ccadic/ESP32-S2-DevBoardTFT/esp32-addons/devshield/images/ESP32-S2-WROOMb.jpg

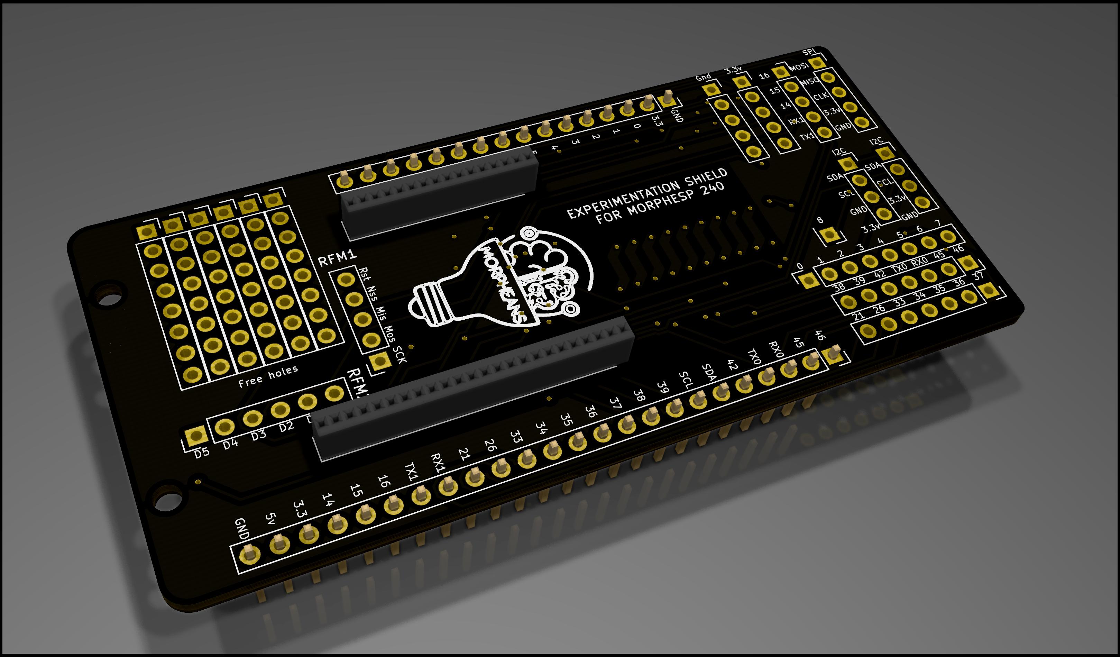
esp32-addons/devshield/images/ESP32-S2-WROOMb.jpg
