ccadic/ESP32-S2-DevBoardTFT/esp32-addons/leather-holder/etui3.JPG

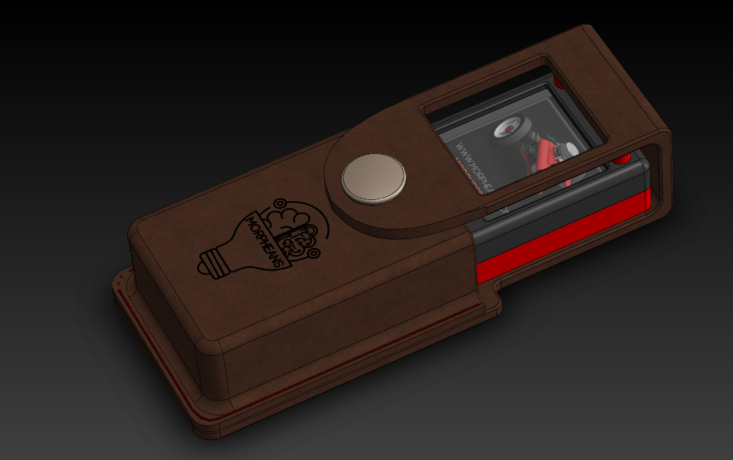
esp32-addons/leather-holder/etui3.JPG
