ccadic/ESP32-S2-DevBoardTFT/esp32-addons/leather-holder/etui4.JPG

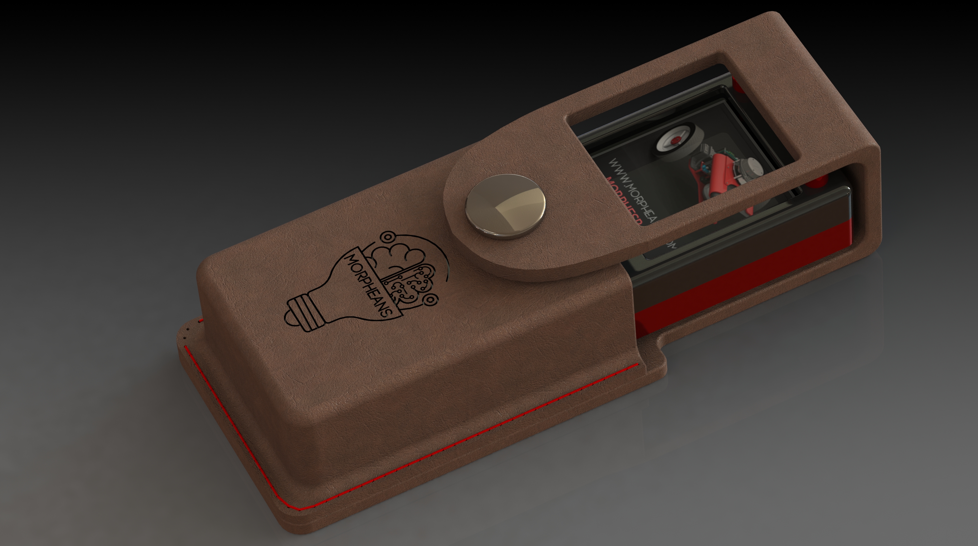
esp32-addons/leather-holder/etui4.JPG
