ccadic/ESP32-S2-DevBoardTFT/photo-gallery/20200802_192520.jpg

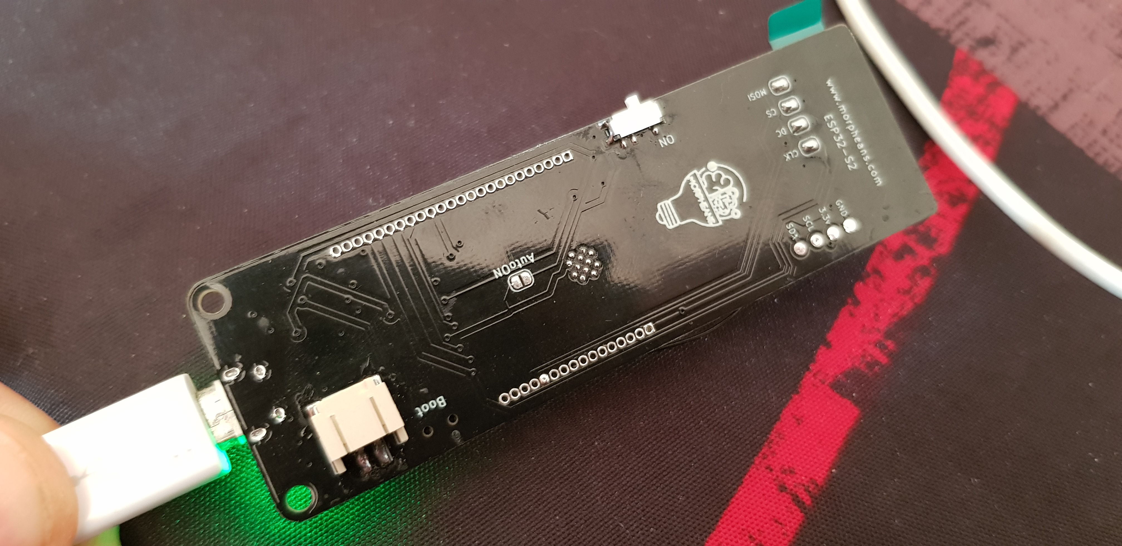
photo-gallery/20200802_192520.jpg
