ccadic/ESP32-S2-DevBoardTFT/photo-gallery/eldiablo2s2.JPG

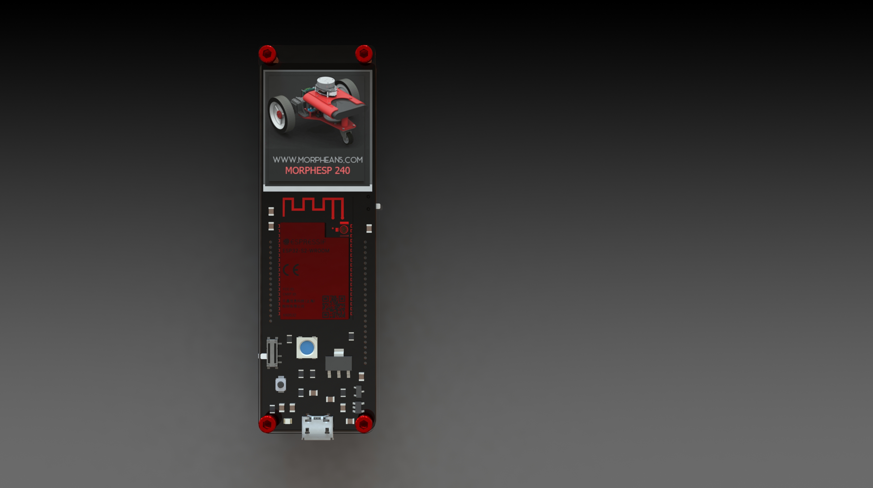
photo-gallery/eldiablo2s2.JPG
