ccadic/ESP32-S2-DevBoardTFT/photo-gallery/eldiablo2s4.JPG

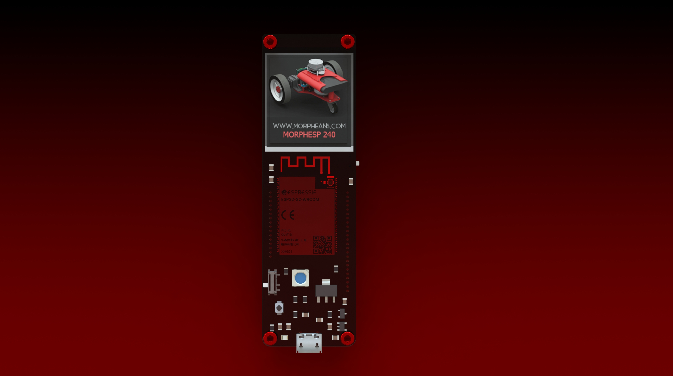
photo-gallery/eldiablo2s4.JPG
