ccadic/ESP32-S2-DevBoardTFT/photo-gallery/ESP32-S2-SOLIDWORKS.JPG

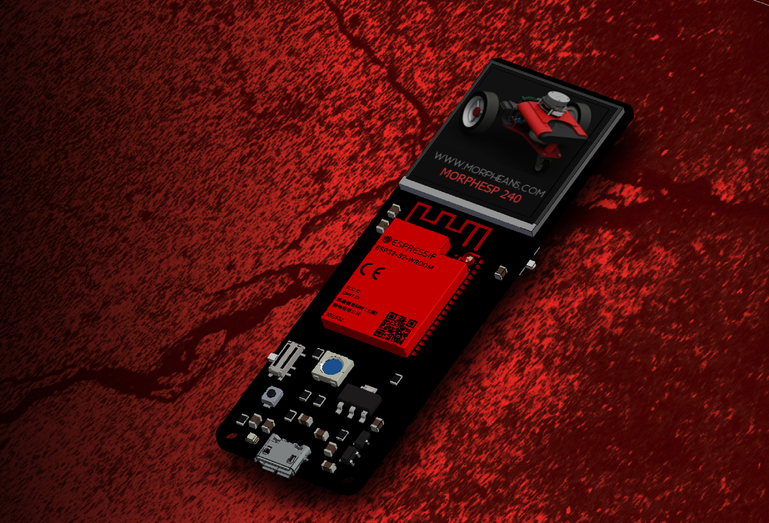
photo-gallery/ESP32-S2-SOLIDWORKS.JPG
