ccadic/ESP32-S2-DevBoardTFT/photo-gallery/etui9.JPG

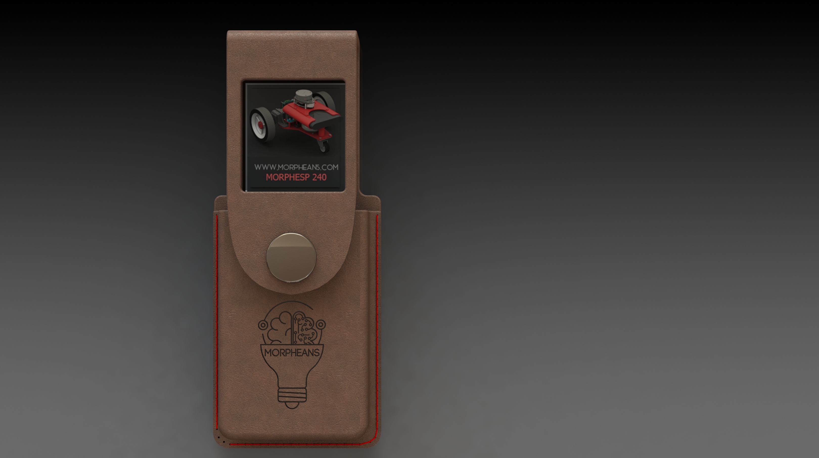
photo-gallery/etui9.JPG
