ccadic/ESP32-S2-DevBoardTFT/photo-gallery/etui11.JPG

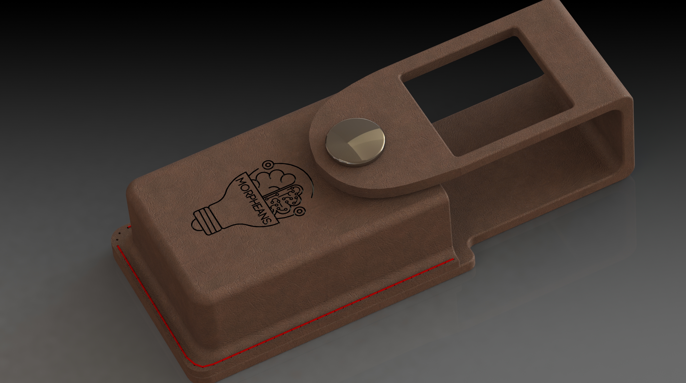
photo-gallery/etui11.JPG
