ccadic/ESP32-S2-DevBoardTFT/photo-gallery/morphesp240-frontside-2-3D rendered.jpg

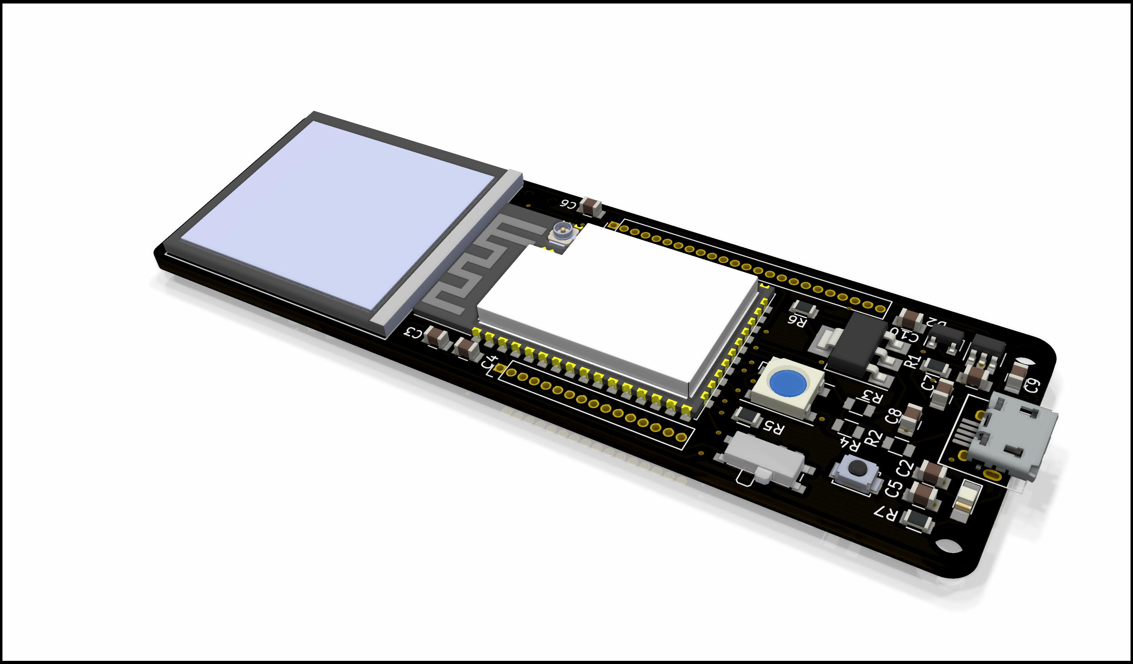
photo-gallery/morphesp240-frontside-2-3D rendered.jpg
