ccadic/ESP32-S2-DevBoardTFT/photo-gallery/morphesp240-pcboard-only.jpg

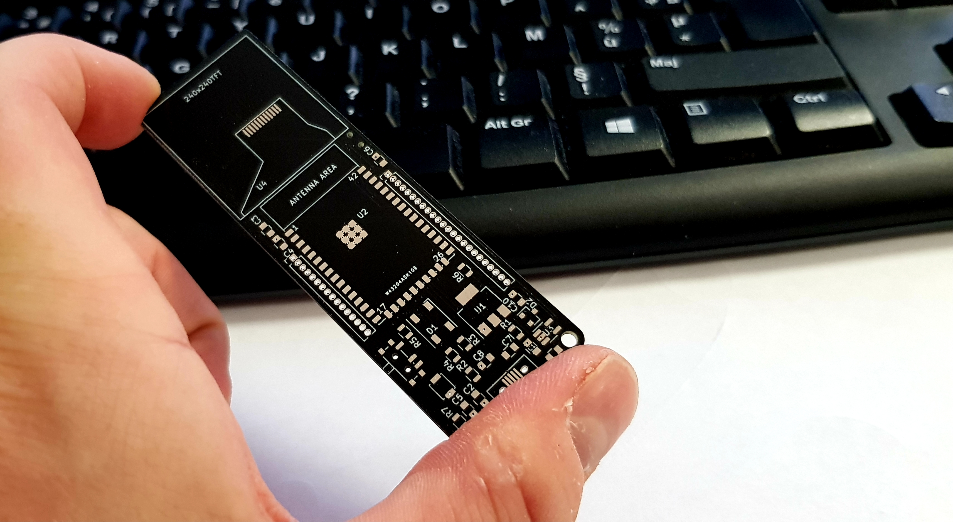
photo-gallery/morphesp240-pcboard-only.jpg
