ccadic/ESP32-S2-DevBoardTFT/esp32-addons/leather-holder/etuit.SLDPRT

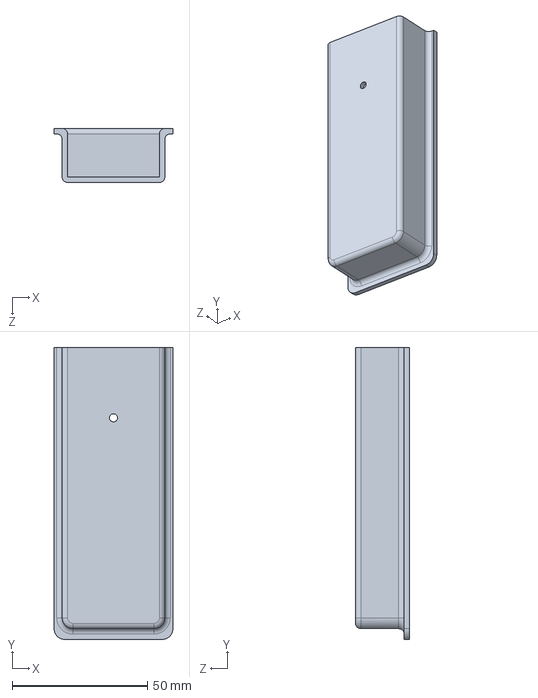
[picture p41: CAD file, 2020-08-18]
esp32-addons/leather-holder/etuit.SLDPRT
44.0 x 108.0 x 20.0 mm
