ccadic/ESP32-S2-DevBoardTFT/hardware/V3.1-LAST/3Dfiles/lipobat.STEP

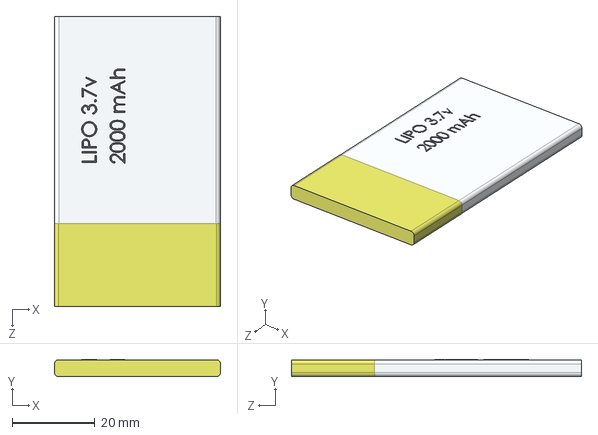
[picture p42: CAD file, 2020-08-18]
hardware/V3.1-LAST/3Dfiles/lipobat.STEP
40.1 x 4.12 x 70.0 mm
