ccadic/ESP32-S2-DevBoardTFT/esp32-addons/leather-holder/Line 20 Eyelet.SLDPRT

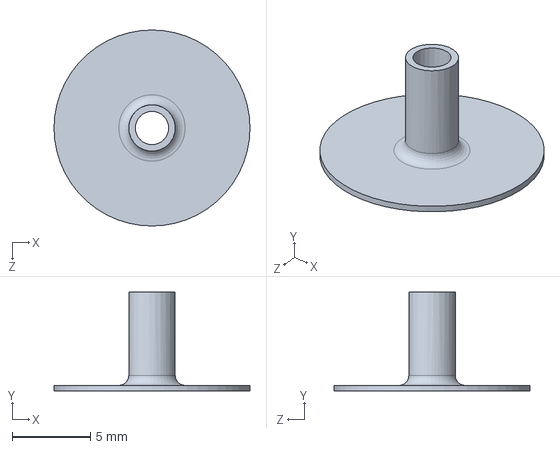
[picture p43: CAD file, 2020-08-18]
esp32-addons/leather-holder/Line 20 Eyelet.SLDPRT
12.5 x 6.32 x 12.5 mm
