ccadic/ESP32-S2-DevBoardTFT/hardware/V3.1-LAST/3Dfiles/JST-PH 2-Pin.STEP

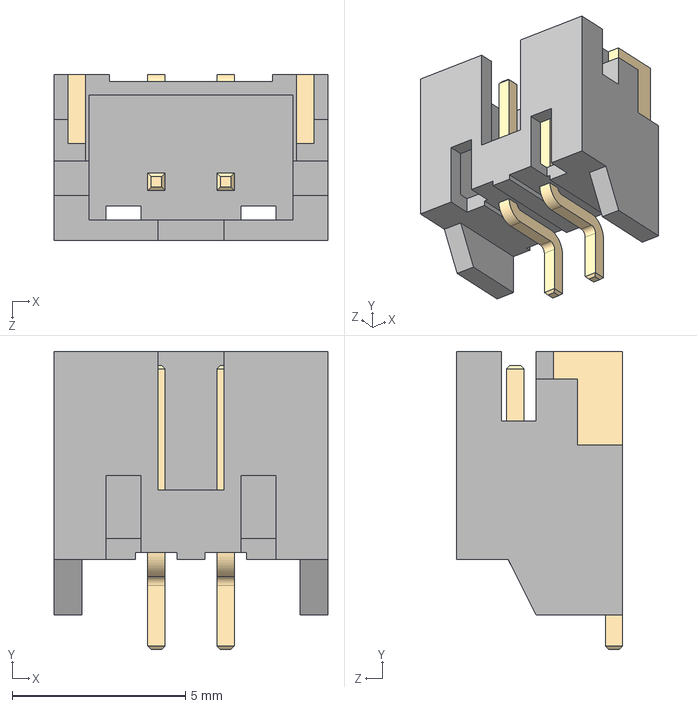
[picture p44: CAD file, 2020-08-18]
hardware/V3.1-LAST/3Dfiles/JST-PH 2-Pin.STEP
7.90 x 8.60 x 4.80 mm
