ccadic/ESP32-S2-DevBoardTFT/esp32-addons/leather-holder/couturecourve3.SLDPRT

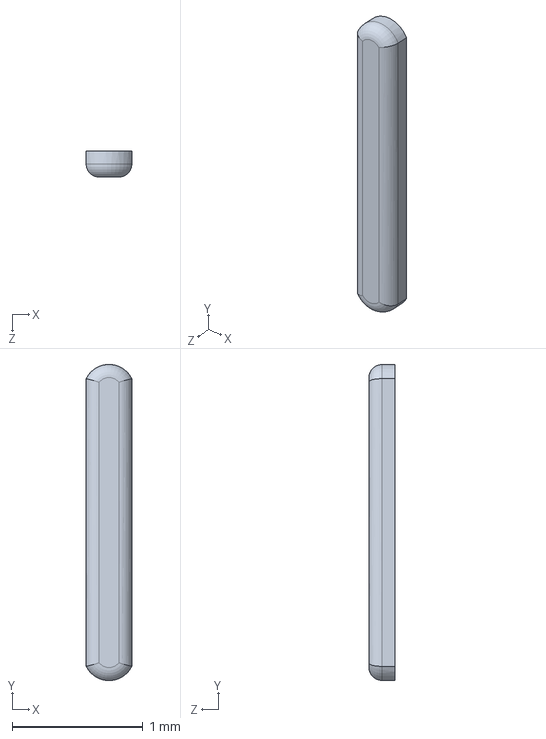
[picture p45: CAD file, 2020-08-18]
esp32-addons/leather-holder/couturecourve3.SLDPRT
0.35 x 2.42 x 0.2 mm
