ccadic/ESP32-S2-DevBoardTFT/esp32-addons/leather-holder/couturecourbe.SLDPRT

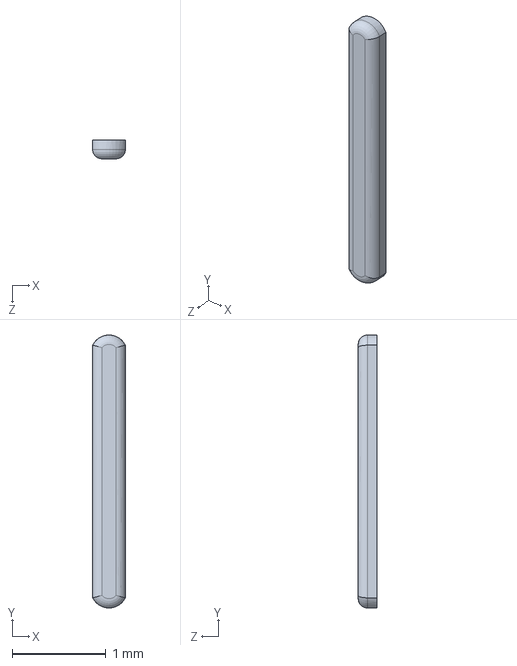
[picture p46: CAD file, 2020-08-18]
esp32-addons/leather-holder/couturecourbe.SLDPRT
0.35 x 2.92 x 0.2 mm
