ccadic/ESP32-S2-DevBoardTFT/hardware/V3.1-LAST/3Dfiles/PCM12SMTR.stp

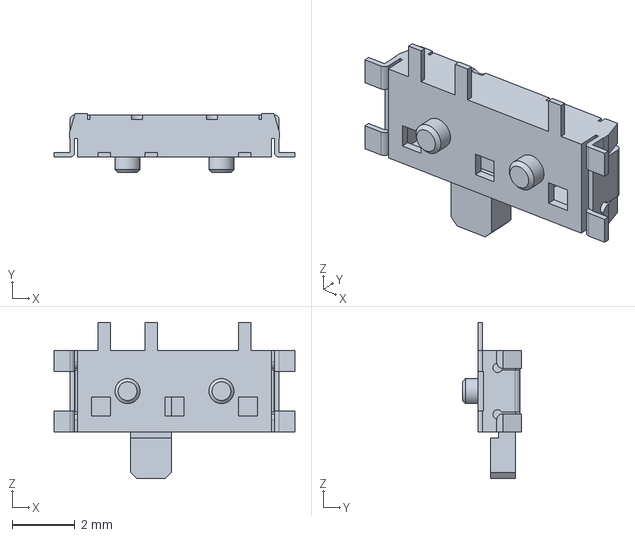
[picture p47: CAD file, 2020-08-18]
hardware/V3.1-LAST/3Dfiles/PCM12SMTR.stp
7.70 x 1.90 x 5.00 mm
