ccadic/ESP32-S2-DevBoardTFT/esp32-addons/leather-holder/Line 20 Cap.SLDPRT

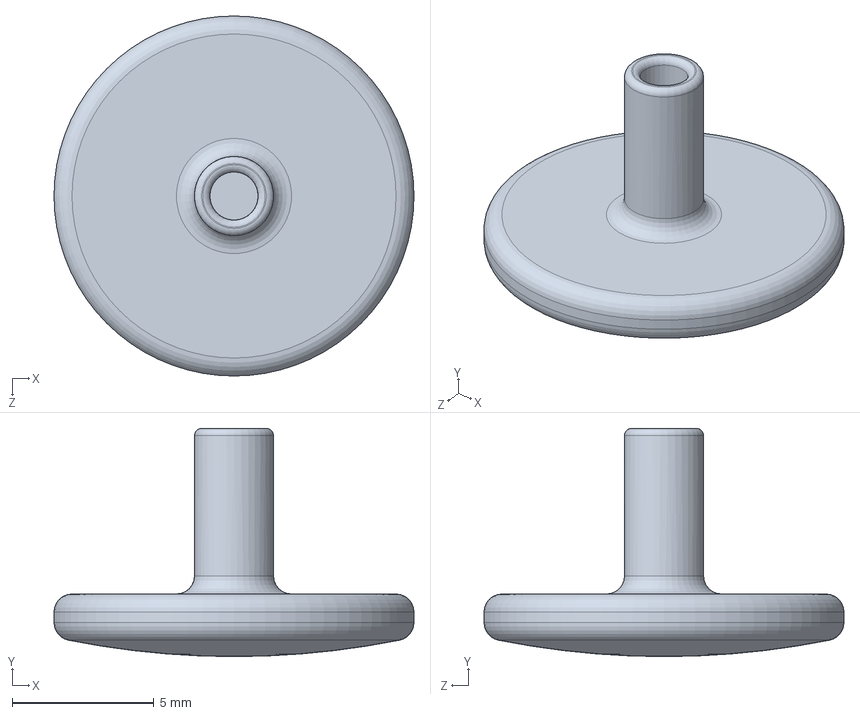
[picture p48: CAD file, 2020-08-18]
esp32-addons/leather-holder/Line 20 Cap.SLDPRT
12.7 x 8.05 x 12.7 mm
