ccadic/ESP32-S2-DevBoardTFT/hardware/V3.1-LAST/3Dfiles/JST-PH 2-Pin Breakout Board.STEP

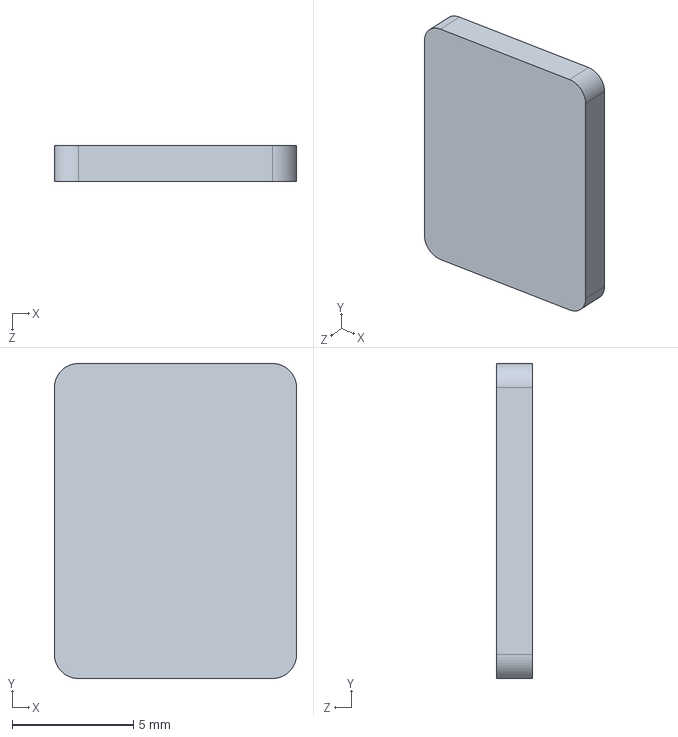
[picture p49: CAD file, 2020-08-18]
hardware/V3.1-LAST/3Dfiles/JST-PH 2-Pin Breakout Board.STEP
10.0 x 13.0 x 1.50 mm
