ccadic/ESP32-S2-DevBoardTFT/esp32-addons/leather-holder/supportcinture.SLDPRT

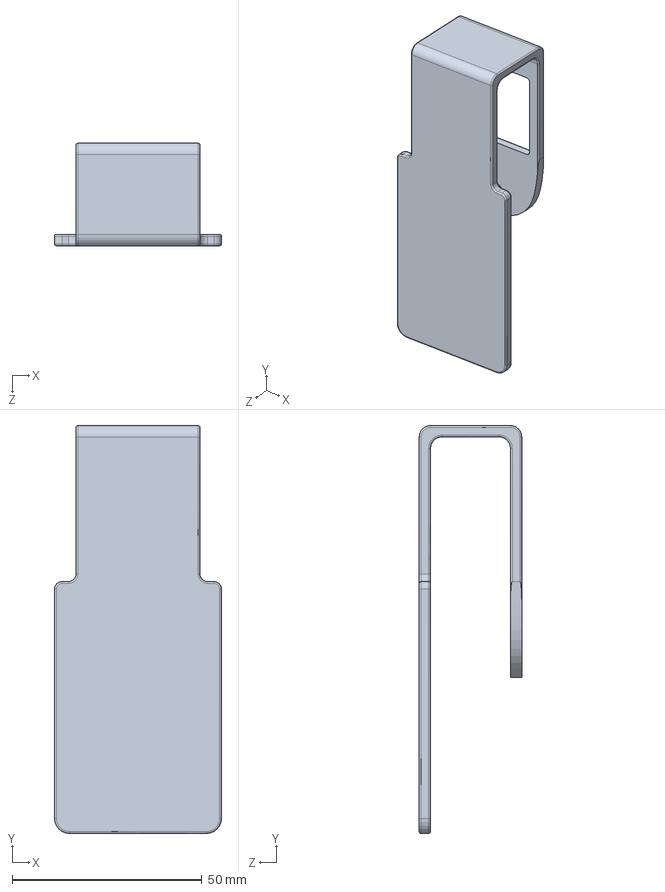
[picture p50: CAD file, 2020-08-18]
esp32-addons/leather-holder/supportcinture.SLDPRT
44.0 x 107.4 x 27.0 mm
