ccadic/ESP32-S2-DevBoardTFT/hardware/V3.1-LAST/3Dfiles/ESP32-S2-WROVER.STEP

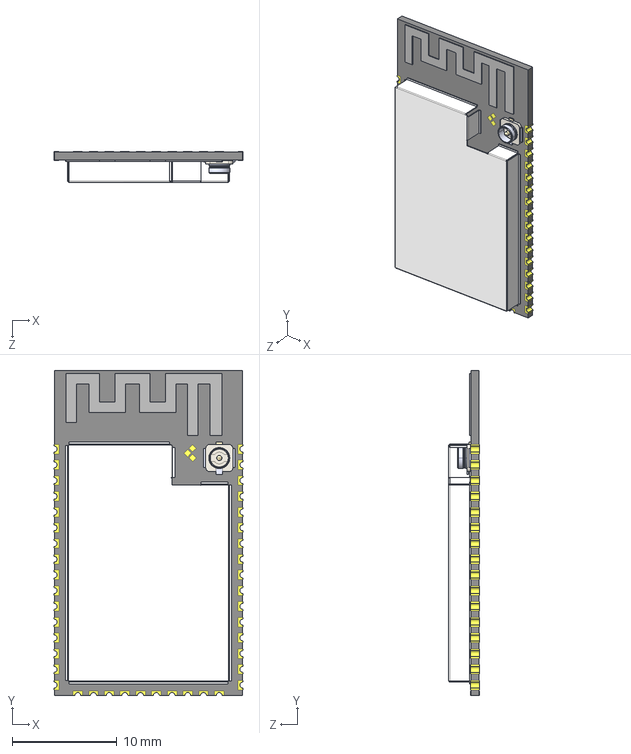
[picture p51: CAD file, 2020-08-02]
hardware/V3.1-LAST/3Dfiles/ESP32-S2-WROVER.STEP
18.0 x 31.0 x 2.91 mm
