ccadic/ESP32-S2-DevBoardTFT/esp32-addons/leather-holder/couture.SLDPRT

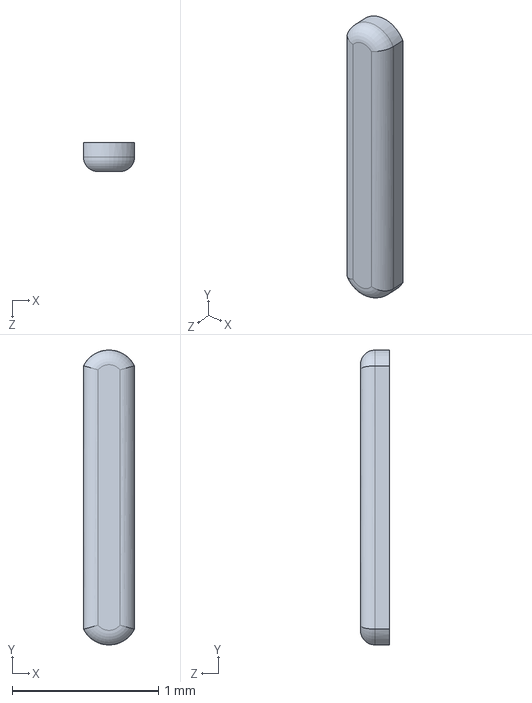
[picture p52: CAD file, 2020-08-18]
esp32-addons/leather-holder/couture.SLDPRT
0.35 x 2.02 x 0.2 mm
