ccadic/ESP32-S2-DevBoardTFT/hardware/V3.1-LAST/3Dfiles/micro_usb_connector.step

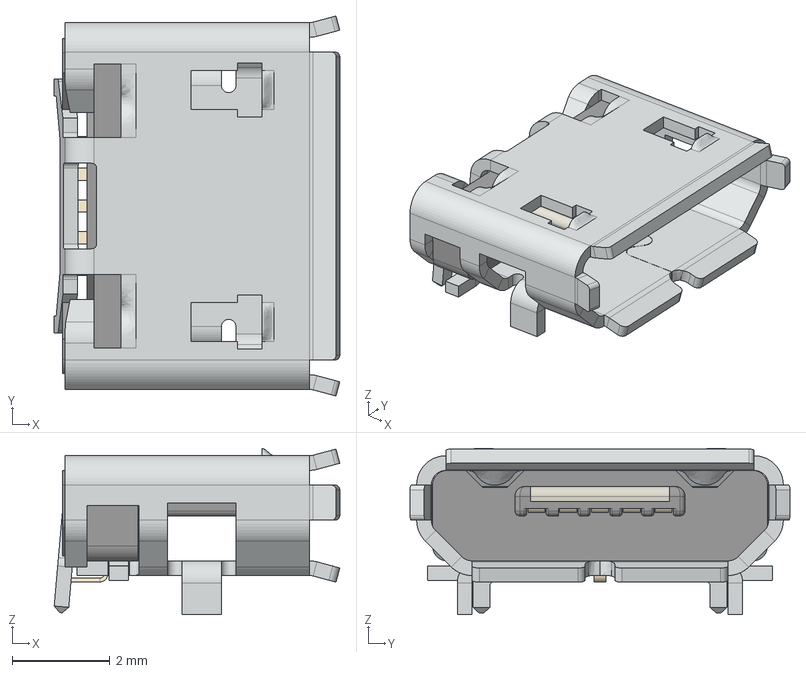
[picture p53: CAD file, 2020-08-02]
hardware/V3.1-LAST/3Dfiles/micro_usb_connector.step
5.84 x 7.77 x 3.40 mm
shield
socket_housing
socket_plate
terminal x 5
