ccadic/ESP32-S2-DevBoardTFT/esp32-addons/leather-holder/couture courbe2.SLDPRT

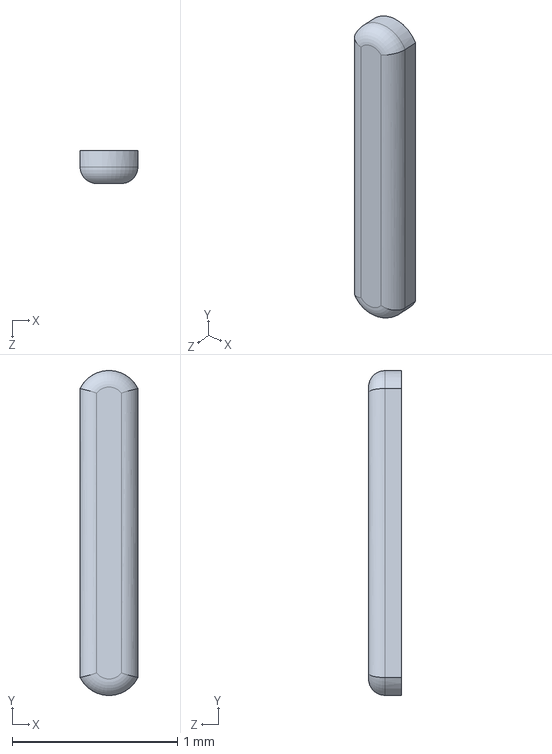
[picture p54: CAD file, 2020-08-18]
esp32-addons/leather-holder/couture courbe2.SLDPRT
0.35 x 1.97 x 0.2 mm
