ccadic/ESP32-S2-DevBoardTFT/hardware/V3.1-LAST/3Dfiles/B3U1000P.step

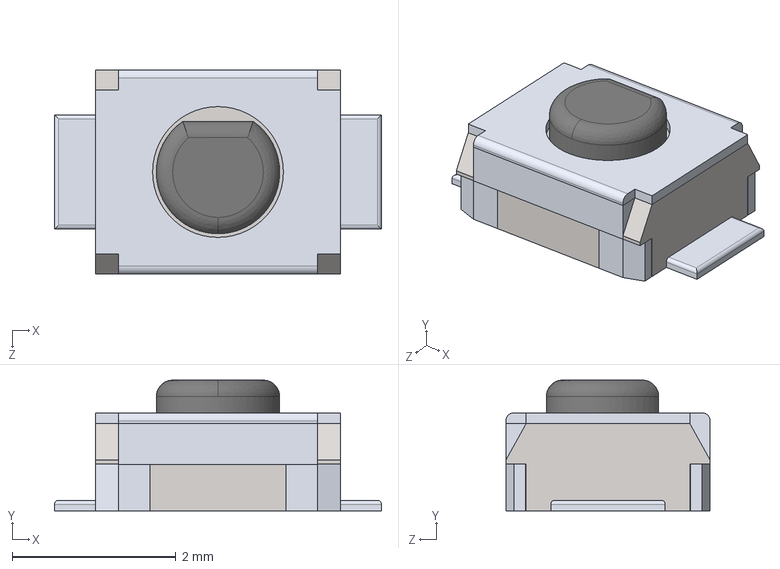
[picture p55: CAD file, 2020-08-02]
hardware/V3.1-LAST/3Dfiles/B3U1000P.step
4.00 x 1.60 x 2.50 mm
