ccadic/ESP32-S2-DevBoardTFT/esp32-addons/leather-holder/Line 20 Stud.SLDPRT

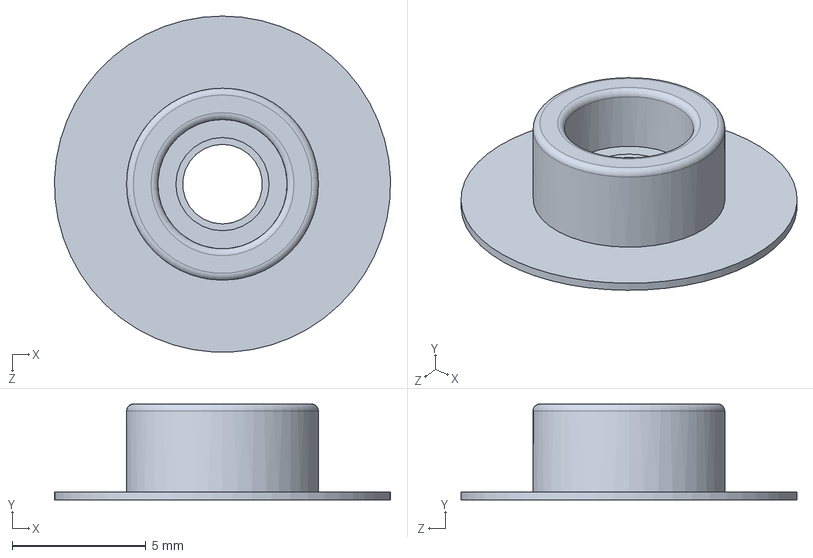
[picture p56: CAD file, 2020-08-18]
esp32-addons/leather-holder/Line 20 Stud.SLDPRT
12.5 x 3.58 x 12.5 mm
