ccadic/ESP32-S2-DevBoardTFT/photo-gallery/morphesp240-assembled2Z2_192531.jpg

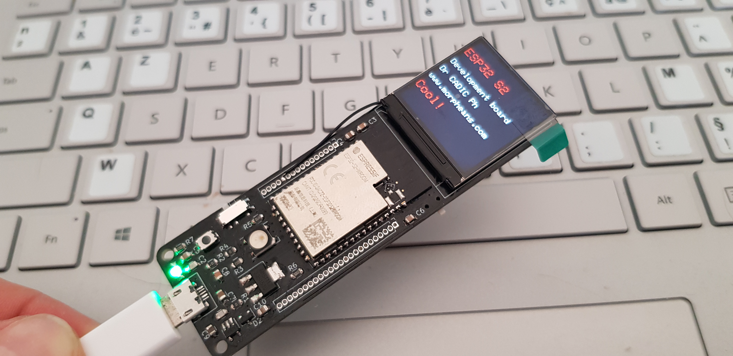
photo-gallery/morphesp240-assembled2Z2_192531.jpg
