ccadic/ESP32-S2-DevBoardTFT/photo-gallery/morphesp240-assembled-3D rendered.jpg

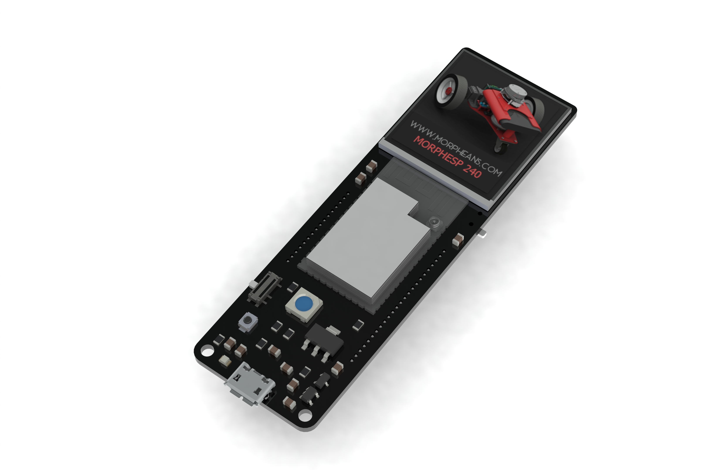
photo-gallery/morphesp240-assembled-3D rendered.jpg
