ccadic/ESP32-S2-DevBoardTFT/photo-gallery/morphesp240-assembled.jpg

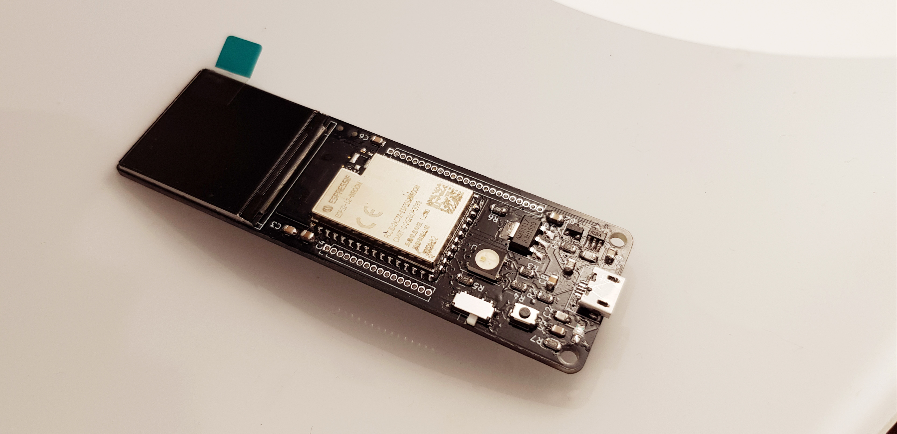
photo-gallery/morphesp240-assembled.jpg
